mawaeg/Sharkropad/docs/_assets/Sharkropad-side-no-led.webp

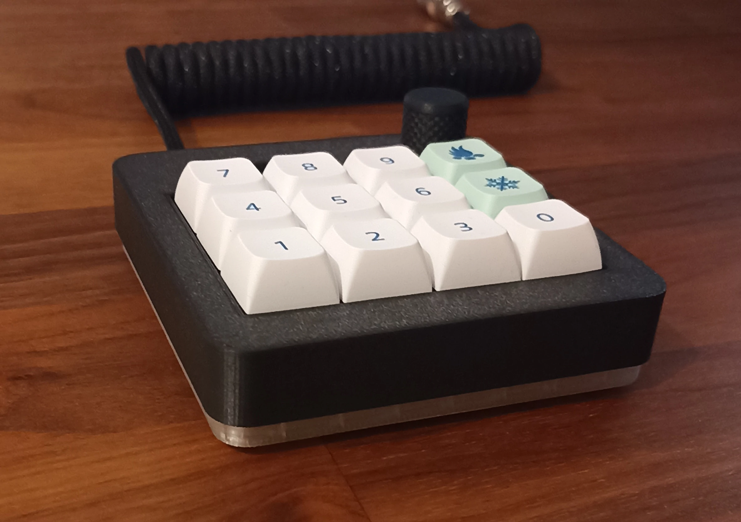
docs/_assets/Sharkropad-side-no-led.webp
